JesseJabezArendse/UCT_ProvisioningJig/Enclosure/Solidworks Model/Straws.SLDPRT

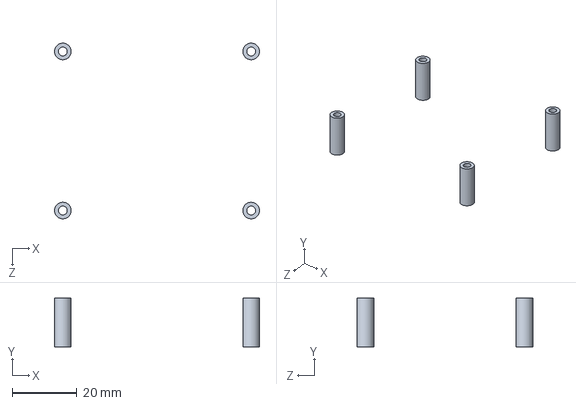
[picture p16: CAD file, 2025-01-05]
Enclosure/Solidworks Model/Straws.SLDPRT
63.1 x 15.0 x 54.1 mm
