JesseJabezArendse/UCT_ProvisioningJig/Enclosure/Solidworks Model/Pogo_pin_P75-E2.stp

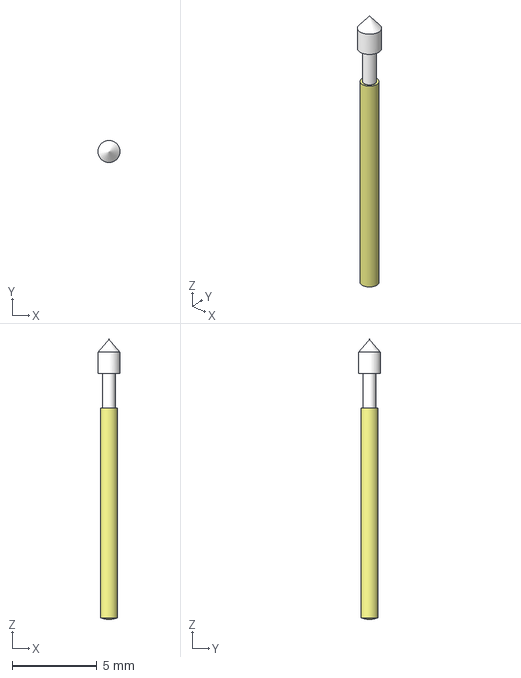
[picture p17: CAD file, 2025-01-05]
Enclosure/Solidworks Model/Pogo_pin_P75-E2.stp
1.30 x 1.30 x 16.5 mm
