JesseJabezArendse/UCT_ProvisioningJig/Enclosure/Solidworks Model/STLink_Cover.SLDPRT

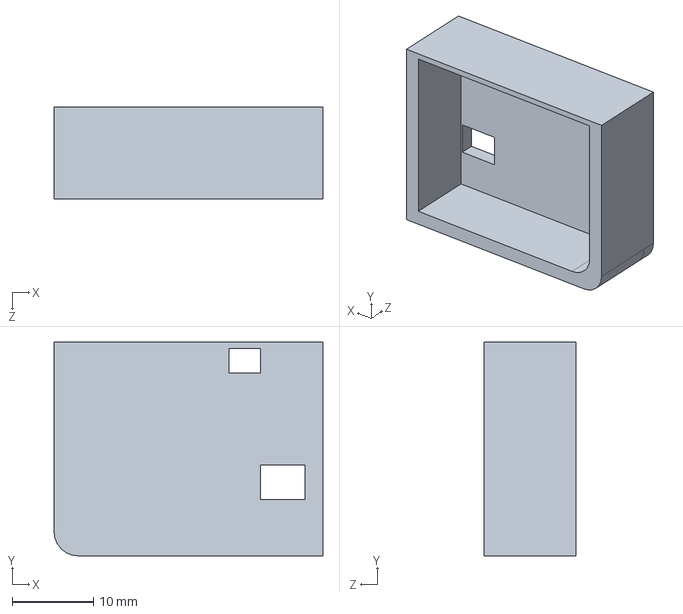
[picture p18: CAD file, 2025-01-05]
Enclosure/Solidworks Model/STLink_Cover.SLDPRT
33.2 x 26.4 x 11.3 mm
