JesseJabezArendse/UCT_ProvisioningJig/Enclosure/Solidworks Model/Rpi components/Raspberry Pi 341.sldprt

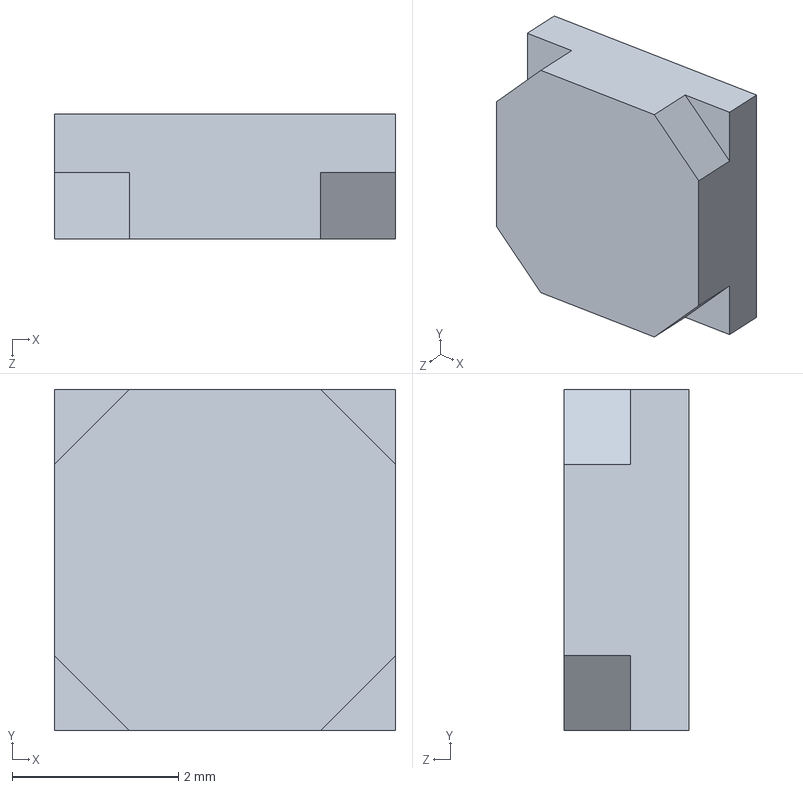
[picture p19: CAD file, 2025-01-05]
Enclosure/Solidworks Model/Rpi components/Raspberry Pi 341.sldprt
4.10 x 4.10 x 1.50 mm
