JesseJabezArendse/UCT_ProvisioningJig/Enclosure/Solidworks Model/Rpi components/molex_0471510001.sldprt

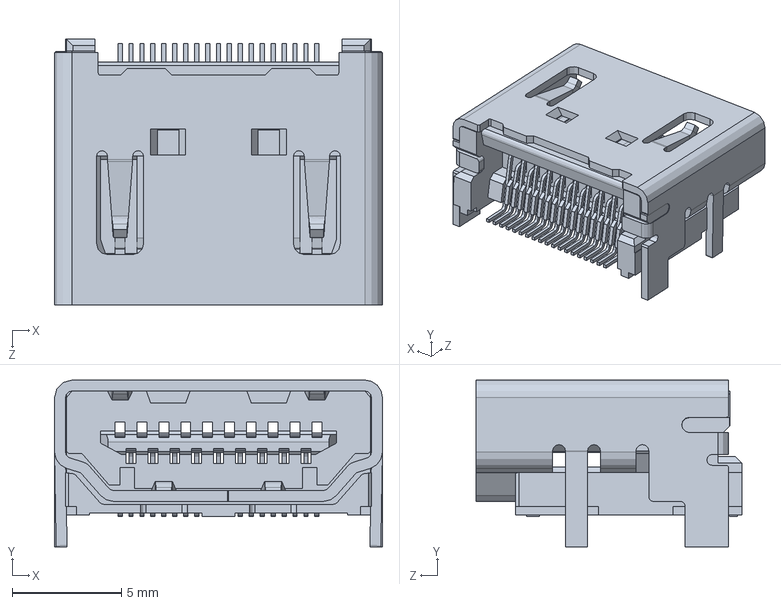
[picture p20: CAD file, 2025-01-05]
Enclosure/Solidworks Model/Rpi components/molex_0471510001.sldprt
15.0 x 7.63 x 12.1 mm
