JesseJabezArendse/UCT_ProvisioningJig/Enclosure/Solidworks Model/Rpi components/Raspberry Pi 3164.sldprt

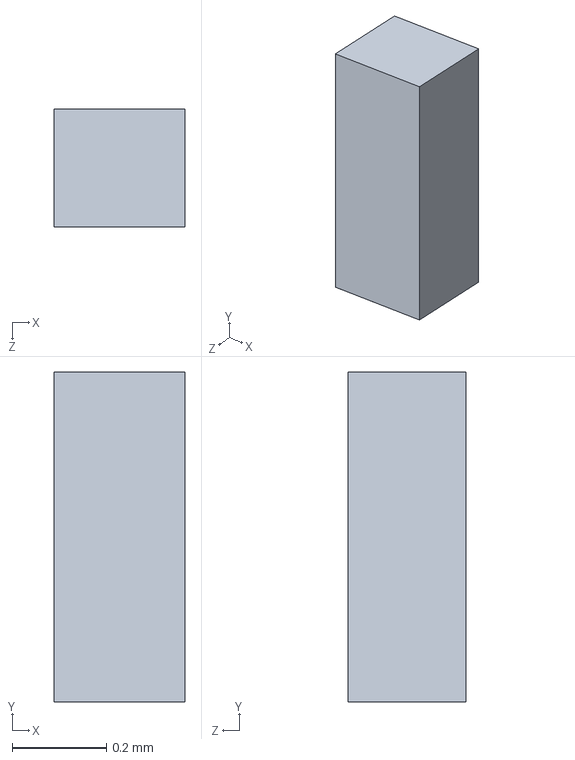
[picture p21: CAD file, 2025-01-05]
Enclosure/Solidworks Model/Rpi components/Raspberry Pi 3164.sldprt
0.278 x 0.7 x 0.25 mm
