JesseJabezArendse/UCT_ProvisioningJig/Enclosure/Solidworks Model/Rpi components/Strait Headers.SLDPRT

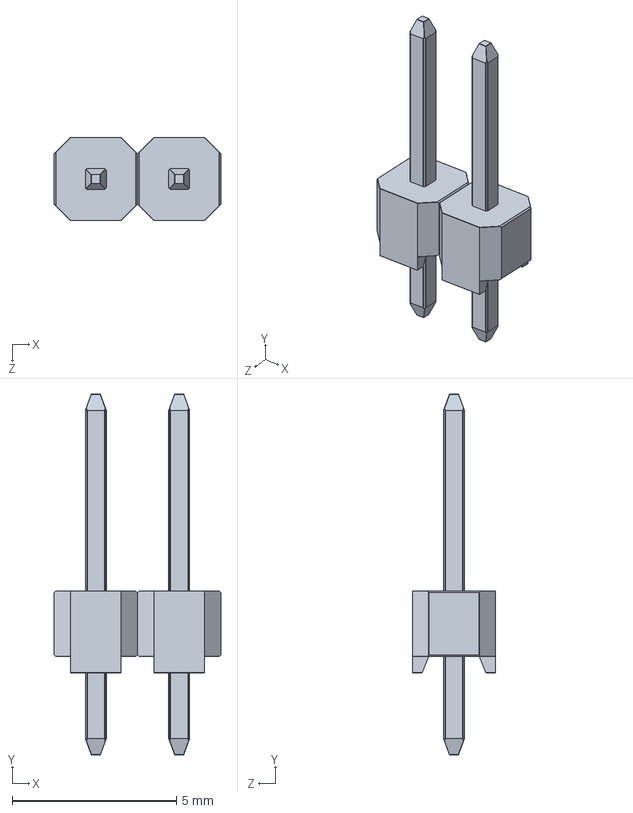
[picture p22: CAD file, 2025-01-05]
Enclosure/Solidworks Model/Rpi components/Strait Headers.SLDPRT
5.08 x 11.0 x 2.54 mm
