JesseJabezArendse/UCT_ProvisioningJig/Enclosure/Solidworks Model/Rpi components/Raspberry Pi 353.sldprt

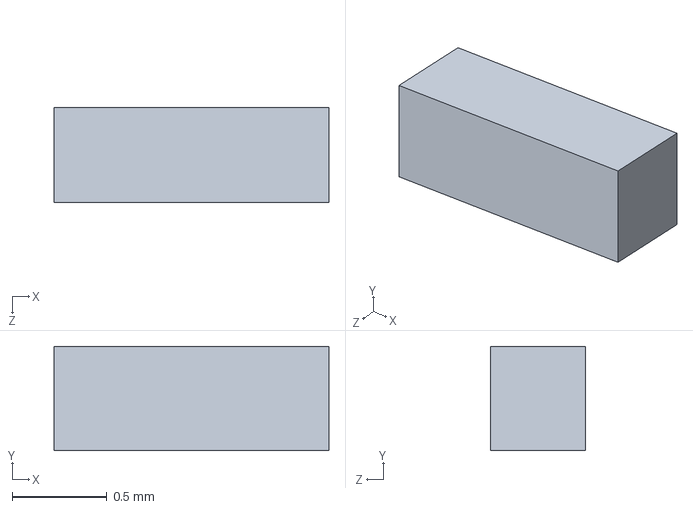
[picture p23: CAD file, 2025-01-05]
Enclosure/Solidworks Model/Rpi components/Raspberry Pi 353.sldprt
1.45 x 0.55 x 0.5 mm
