JesseJabezArendse/UCT_ProvisioningJig/Enclosure/Solidworks Model/Rpi components/Solder2.sldprt

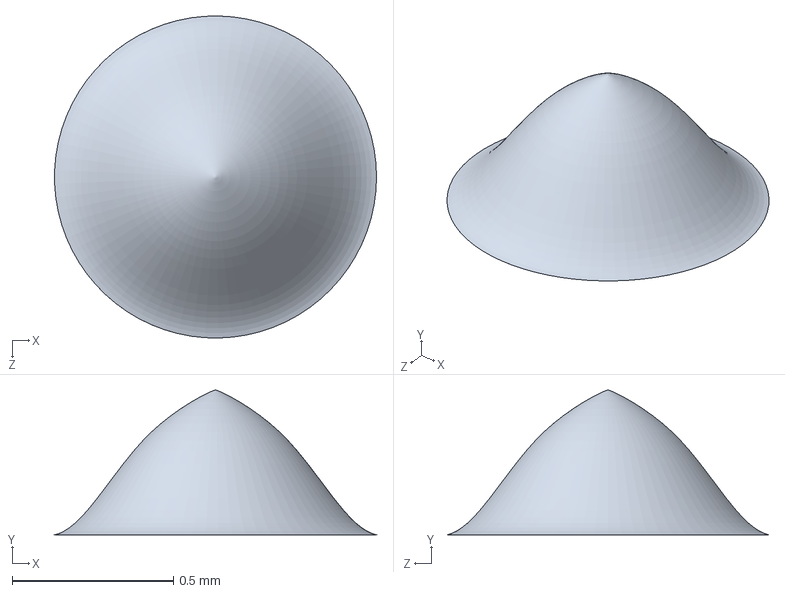
[picture p24: CAD file, 2025-01-05]
Enclosure/Solidworks Model/Rpi components/Solder2.sldprt
1.00 x 0.45 x 1 mm
