JesseJabezArendse/UCT_ProvisioningJig/Enclosure/Solidworks Model/Rpi components/Raspberry Pi 332.sldprt

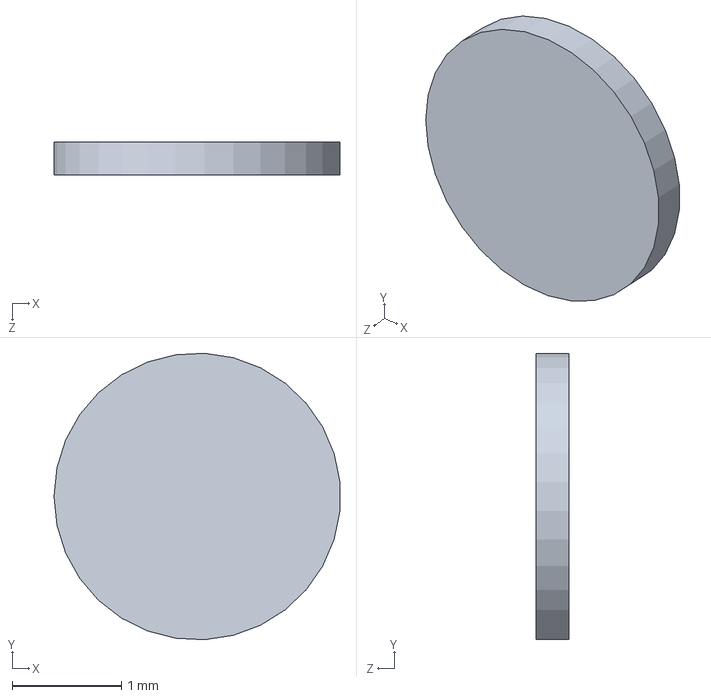
[picture p25: CAD file, 2025-01-05]
Enclosure/Solidworks Model/Rpi components/Raspberry Pi 332.sldprt
2.62 x 2.63 x 0.3 mm
