JesseJabezArendse/UCT_ProvisioningJig/Enclosure/Solidworks Model/Rpi components/Raspberry Pi 334.sldprt

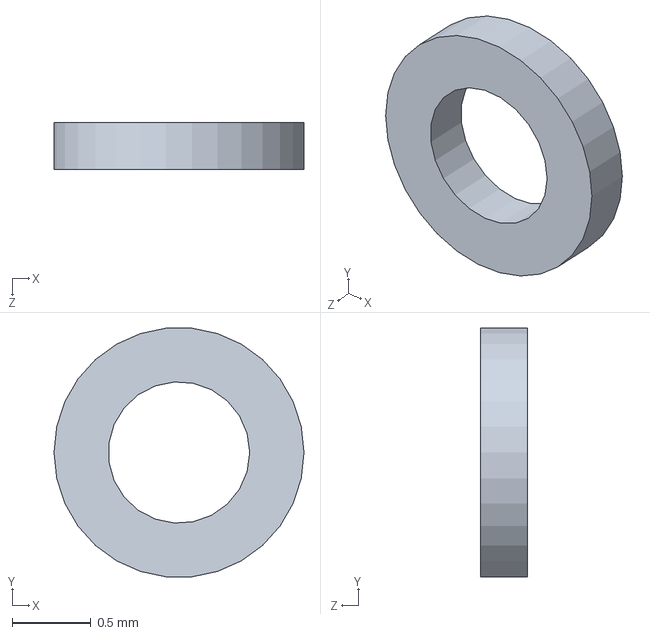
[picture p26: CAD file, 2025-01-05]
Enclosure/Solidworks Model/Rpi components/Raspberry Pi 334.sldprt
1.59 x 1.58 x 0.3 mm
