JesseJabezArendse/UCT_ProvisioningJig/Enclosure/Solidworks Model/Rpi components/Raspberry Pi 336.sldprt

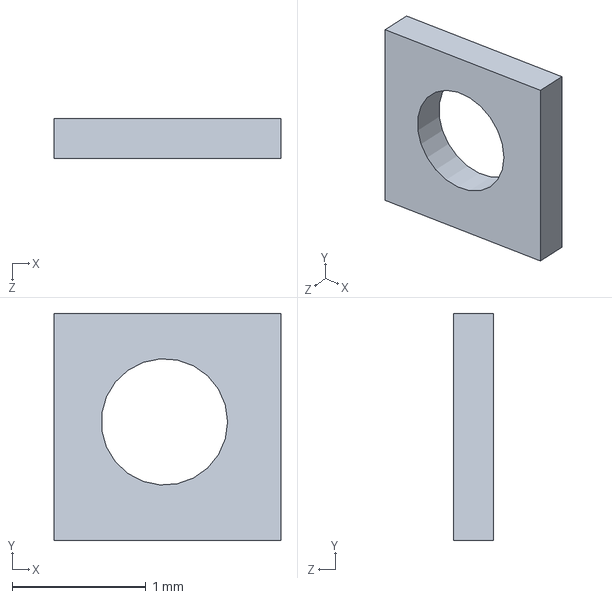
[picture p27: CAD file, 2025-01-05]
Enclosure/Solidworks Model/Rpi components/Raspberry Pi 336.sldprt
1.70 x 1.70 x 0.3 mm
