JesseJabezArendse/UCT_ProvisioningJig/Enclosure/Solidworks Model/Rpi components/Raspberry Pi 312.sldprt

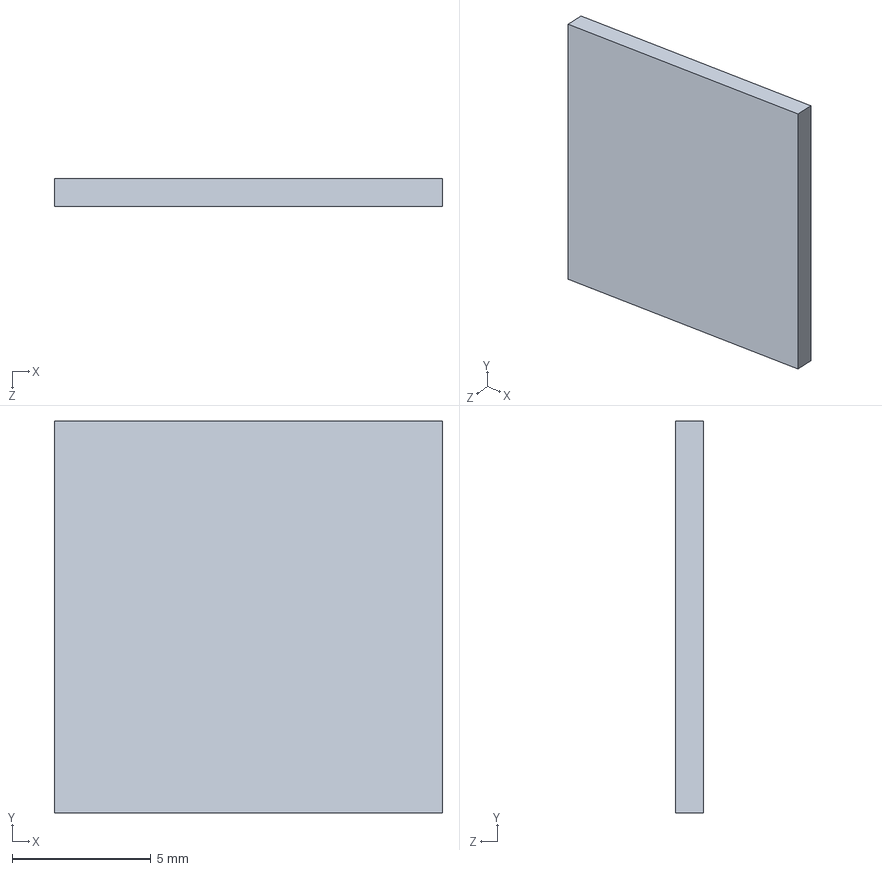
[picture p28: CAD file, 2025-01-05]
Enclosure/Solidworks Model/Rpi components/Raspberry Pi 312.sldprt
14.0 x 14.1 x 1.00 mm
