JesseJabezArendse/UCT_ProvisioningJig/Enclosure/Solidworks Model/Rpi components/HANRUN2_HR911105A.sldprt

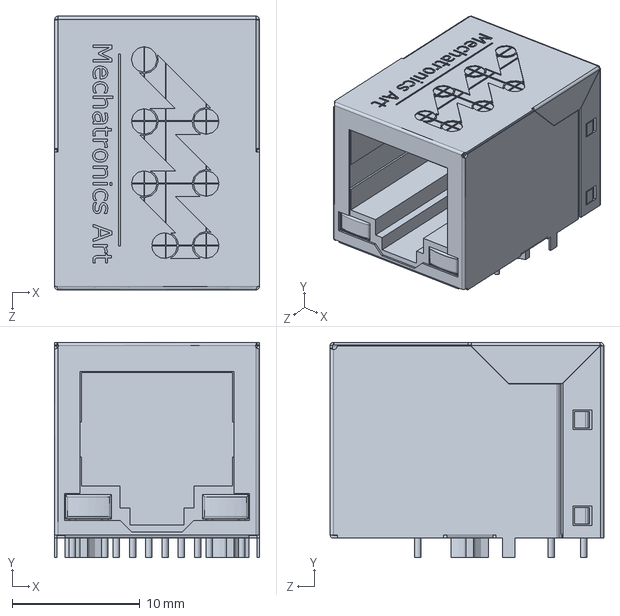
[picture p29: CAD file, 2025-01-05]
Enclosure/Solidworks Model/Rpi components/HANRUN2_HR911105A.sldprt
16.0 x 16.8 x 21.4 mm
